ChanceFleeting/Fleeting_BMEDesign/Semester1Design/Electronics/FlowChart_v1.JPG

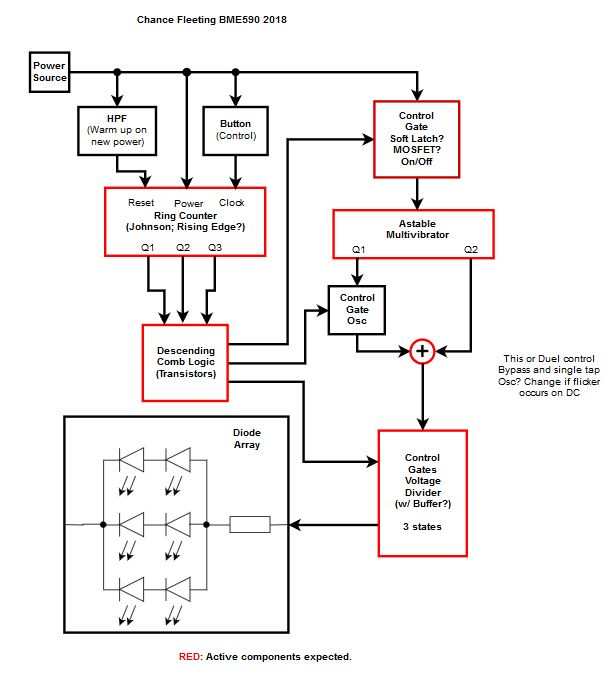
Semester1Design/Electronics/FlowChart_v1.JPG
