ChanceFleeting/Fleeting_BMEDesign/Semester1Design/Electronics/FlowChart_v2.jpg

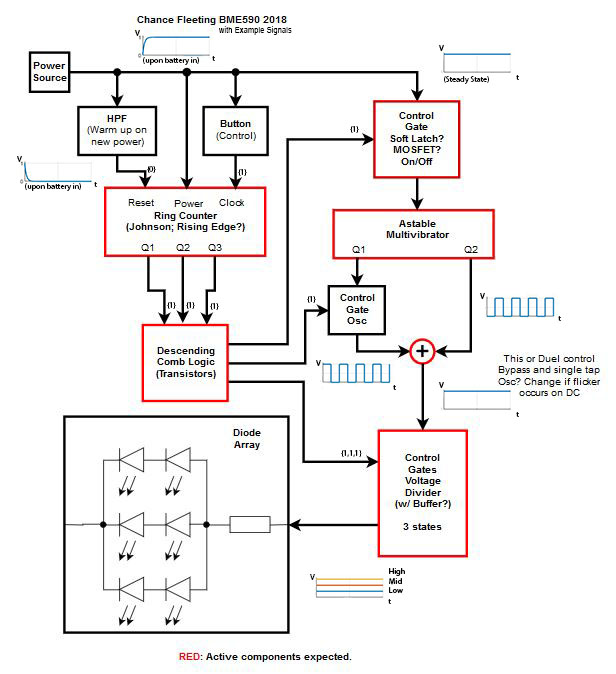
Semester1Design/Electronics/FlowChart_v2.jpg
