ChanceFleeting/Fleeting_BMEDesign/Semester1Design/Electronics/PCB/PCB_2D_Front.PNG

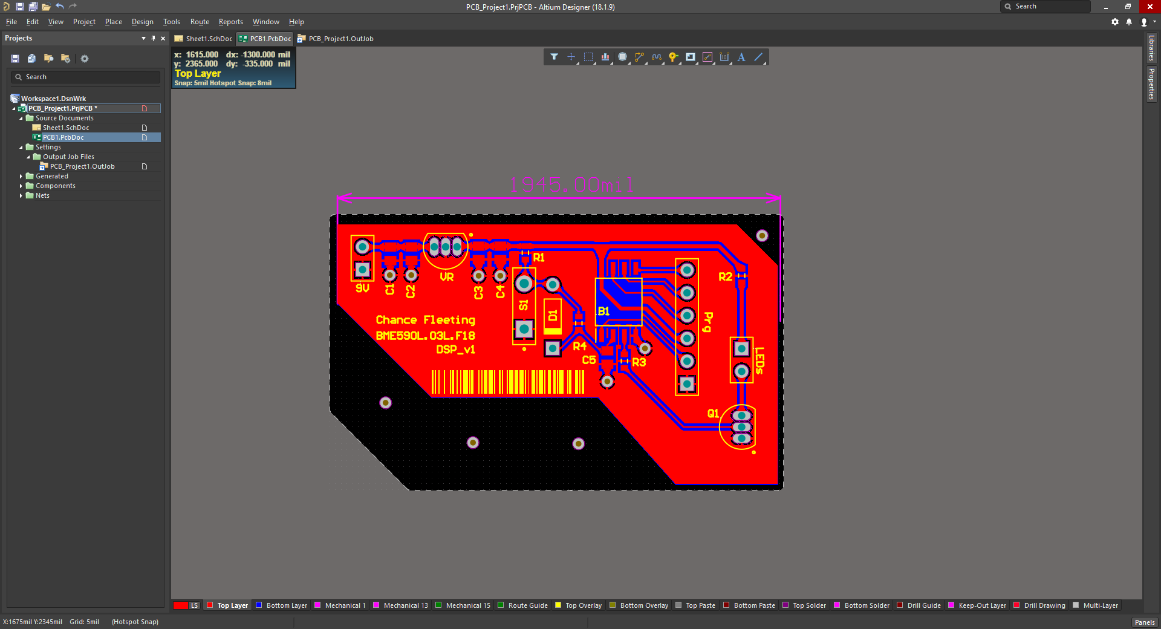
Semester1Design/Electronics/PCB/PCB_2D_Front.PNG
