ChanceFleeting/Fleeting_BMEDesign/Semester1Design/Electronics/PCB/PCB_2D_Front_smaller.PNG

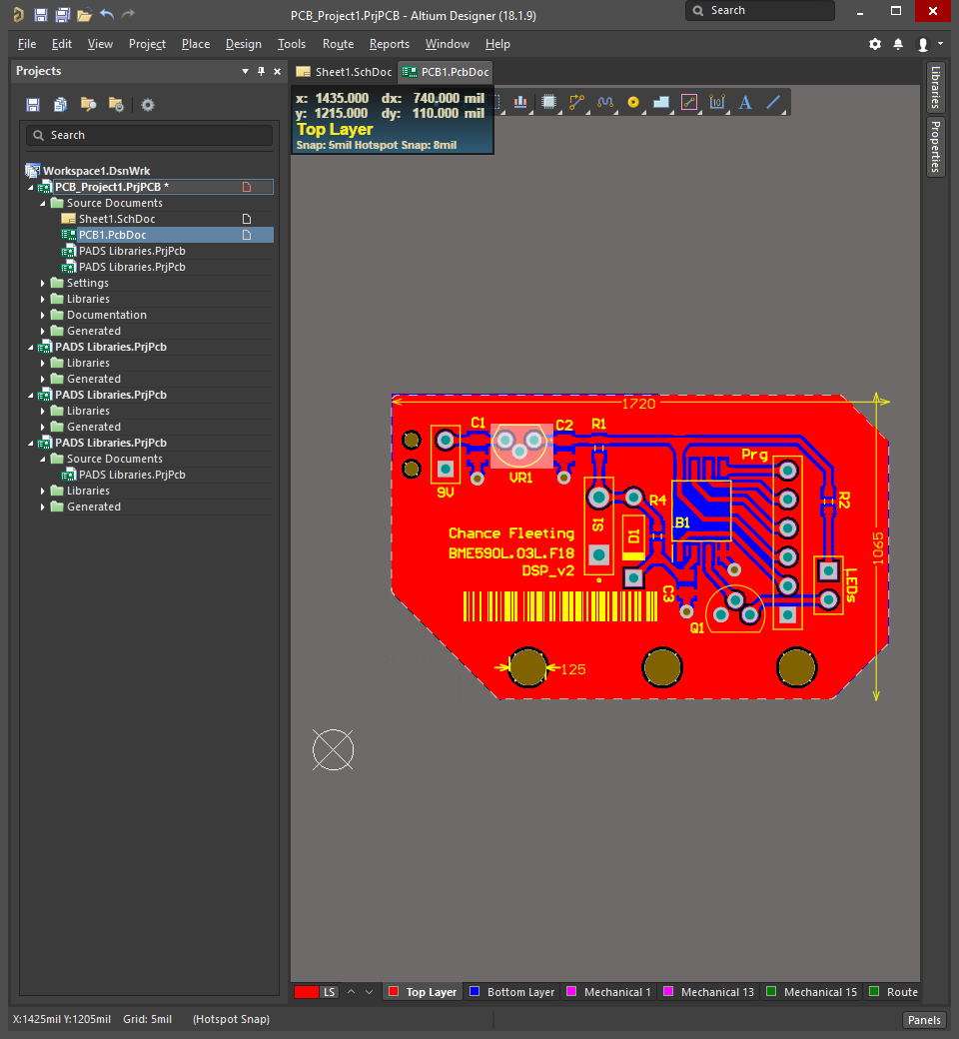
Semester1Design/Electronics/PCB/PCB_2D_Front_smaller.PNG
