ChanceFleeting/Fleeting_BMEDesign/Semester1Design/Electronics/PCB/PCB_3D_Back.PNG

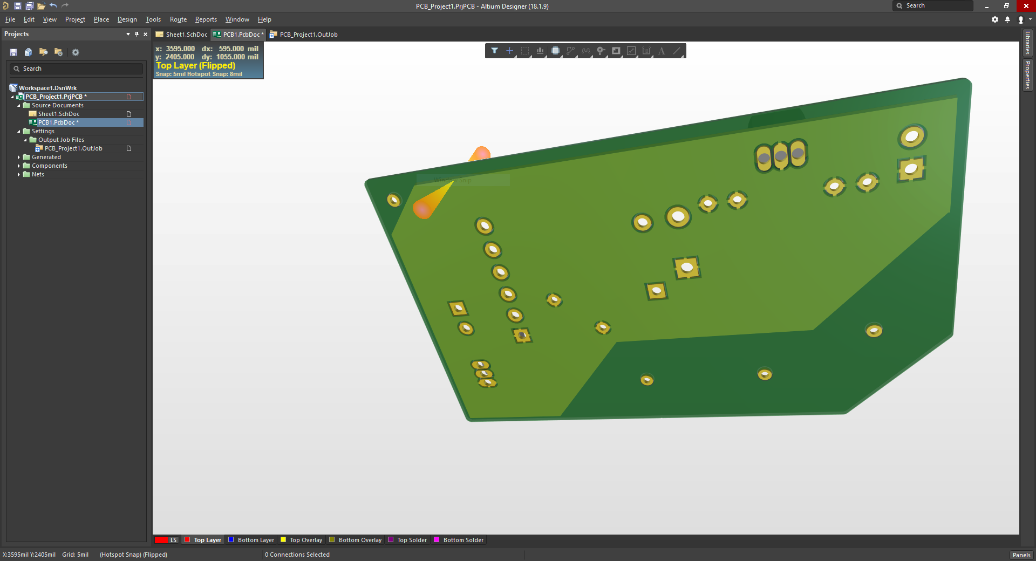
Semester1Design/Electronics/PCB/PCB_3D_Back.PNG
