ChanceFleeting/Fleeting_BMEDesign/Semester1Design/Electronics/PCB/PCB_3D_Back_smaller.PNG

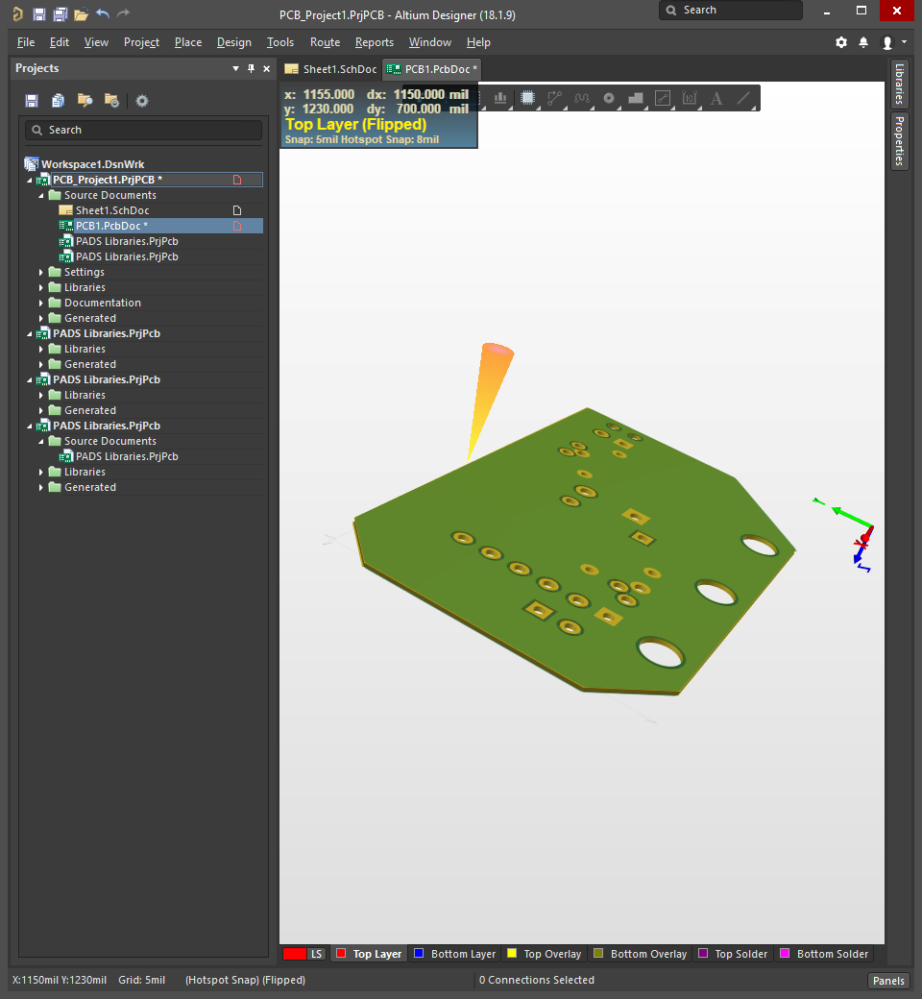
Semester1Design/Electronics/PCB/PCB_3D_Back_smaller.PNG
