ChanceFleeting/Fleeting_BMEDesign/Semester1Design/Mechanical/3Drendering.JPG

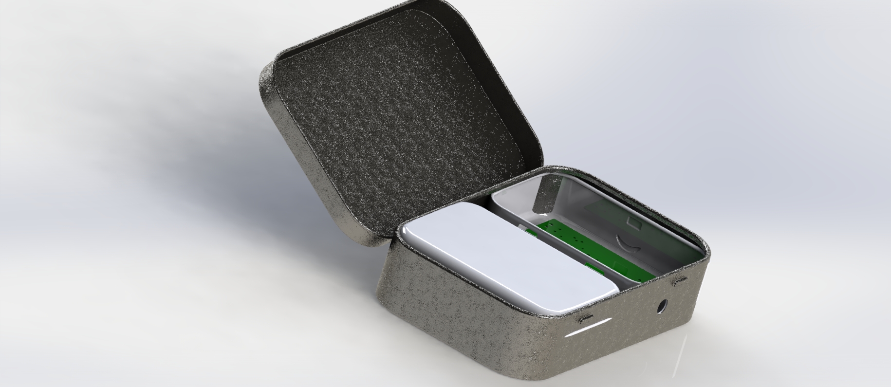
Semester1Design/Mechanical/3Drendering.JPG
