ChanceFleeting/Fleeting_BMEDesign/Semester1Design/Mechanical/MechSchem.jpeg

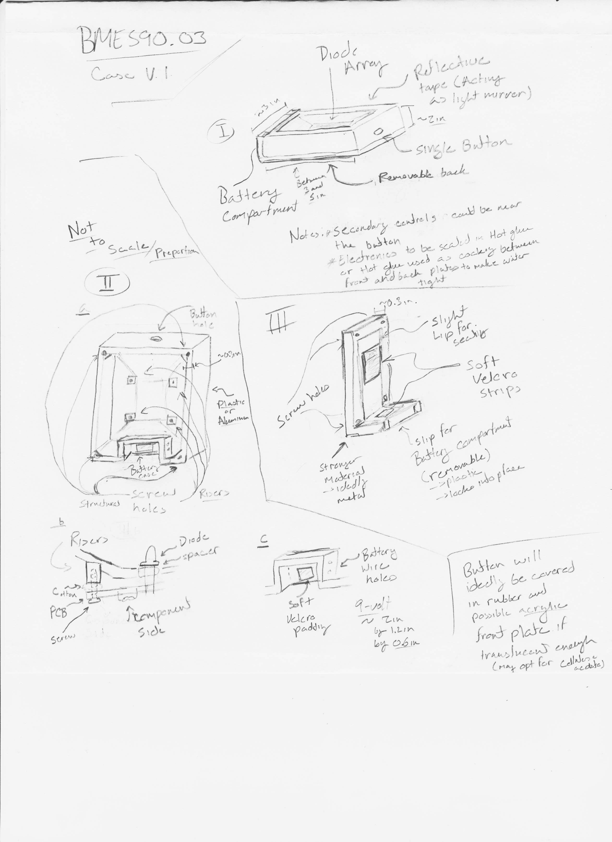
Semester1Design/Mechanical/MechSchem.jpeg
