ChanceFleeting/Fleeting_BMEDesign/Semester1Design/Software/CodingScheme1.PNG

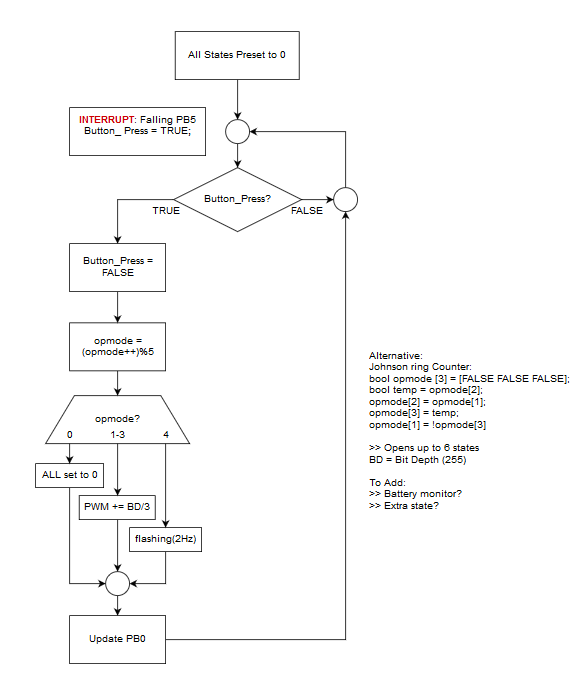
Semester1Design/Software/CodingScheme1.PNG
