ChanceFleeting/Fleeting_BMEDesign/Semester1Design/Testing/Final_Design_Large.jpg

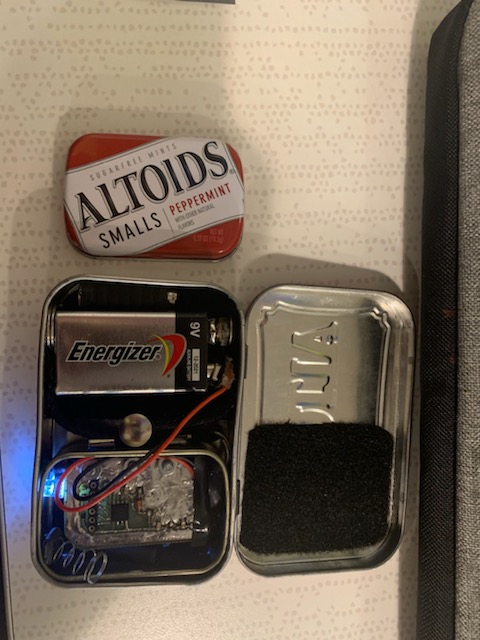
Semester1Design/Testing/Final_Design_Large.jpg
