ChanceFleeting/Fleeting_BMEDesign/Semester1Design/Testing/Final_Design_Large_2.jpg

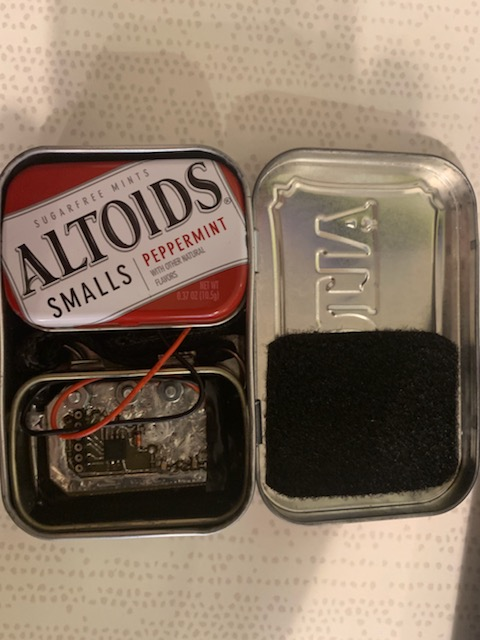
Semester1Design/Testing/Final_Design_Large_2.jpg
