ChanceFleeting/Fleeting_BMEDesign/Semester1Design/Testing/Final_Design_Small.jpg

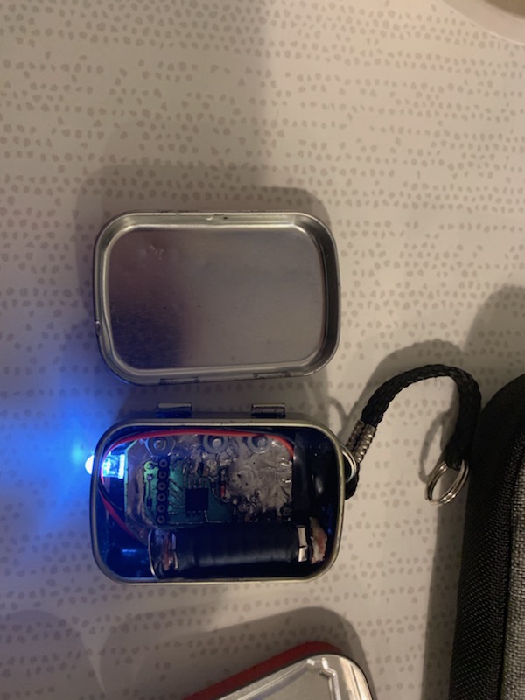
Semester1Design/Testing/Final_Design_Small.jpg
