ChanceFleeting/Fleeting_BMEDesign/Semester1Design/Testing/Final_Design_Small_2.jpg

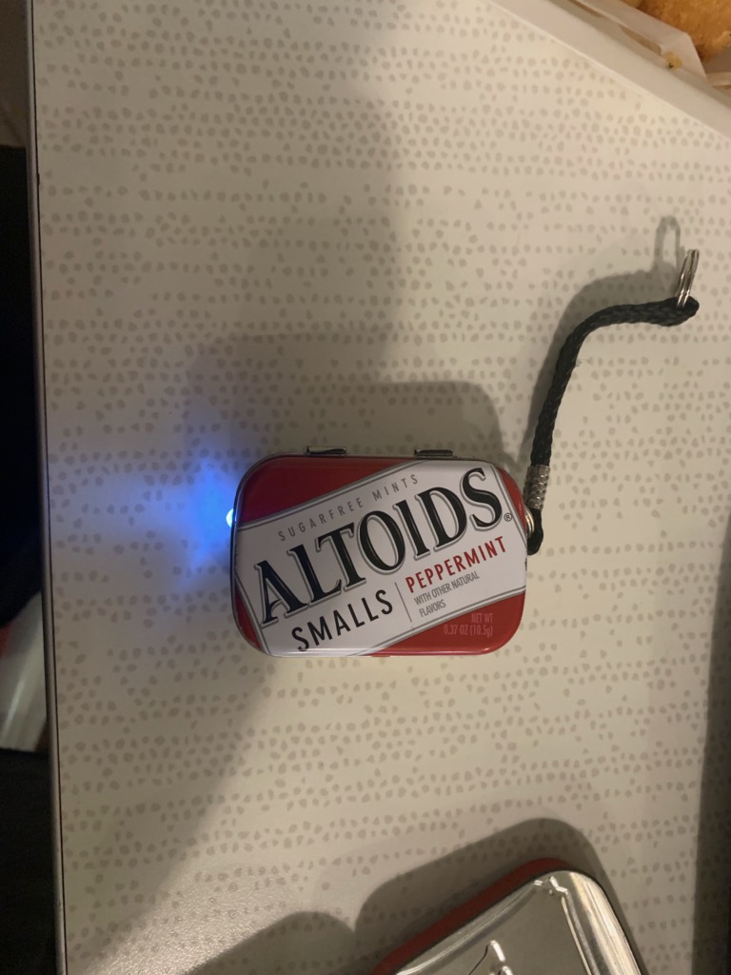
Semester1Design/Testing/Final_Design_Small_2.jpg
