ChanceFleeting/Fleeting_BMEDesign/Semester1Design/Testing/47579365_2035901176702119_994453910217293824_n.jpg

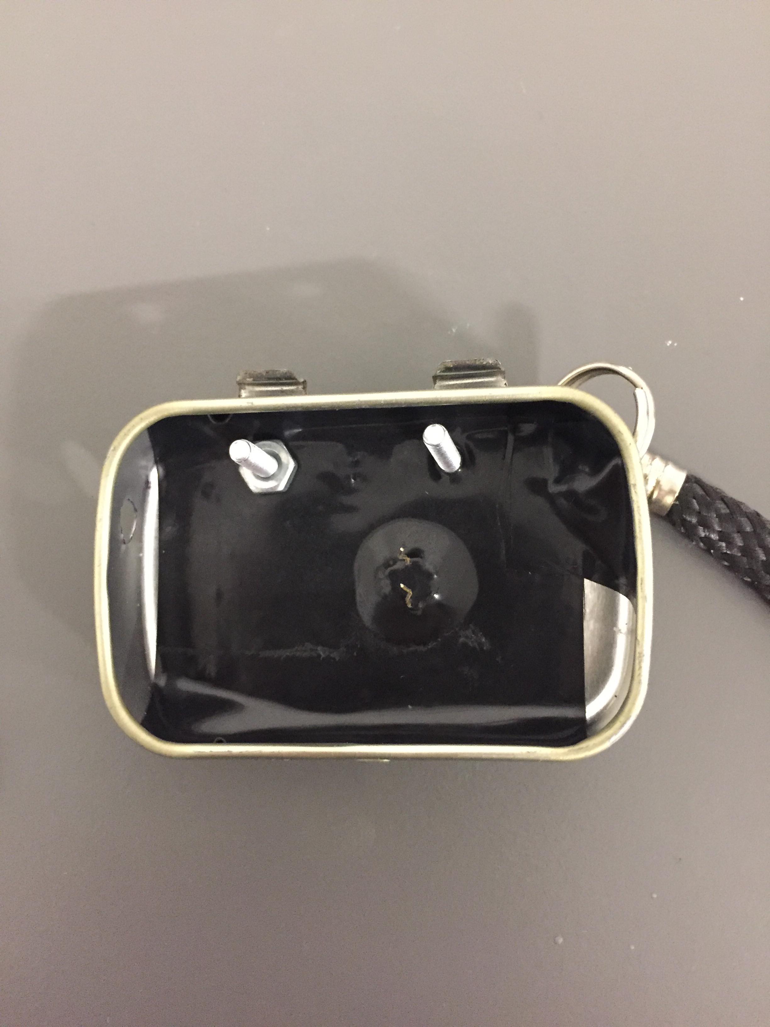
Semester1Design/Testing/47579365_2035901176702119_994453910217293824_n.jpg
