ChanceFleeting/Fleeting_BMEDesign/Semester1Design/Testing/47679753_585677868552466_7844225675530600448_n.jpg

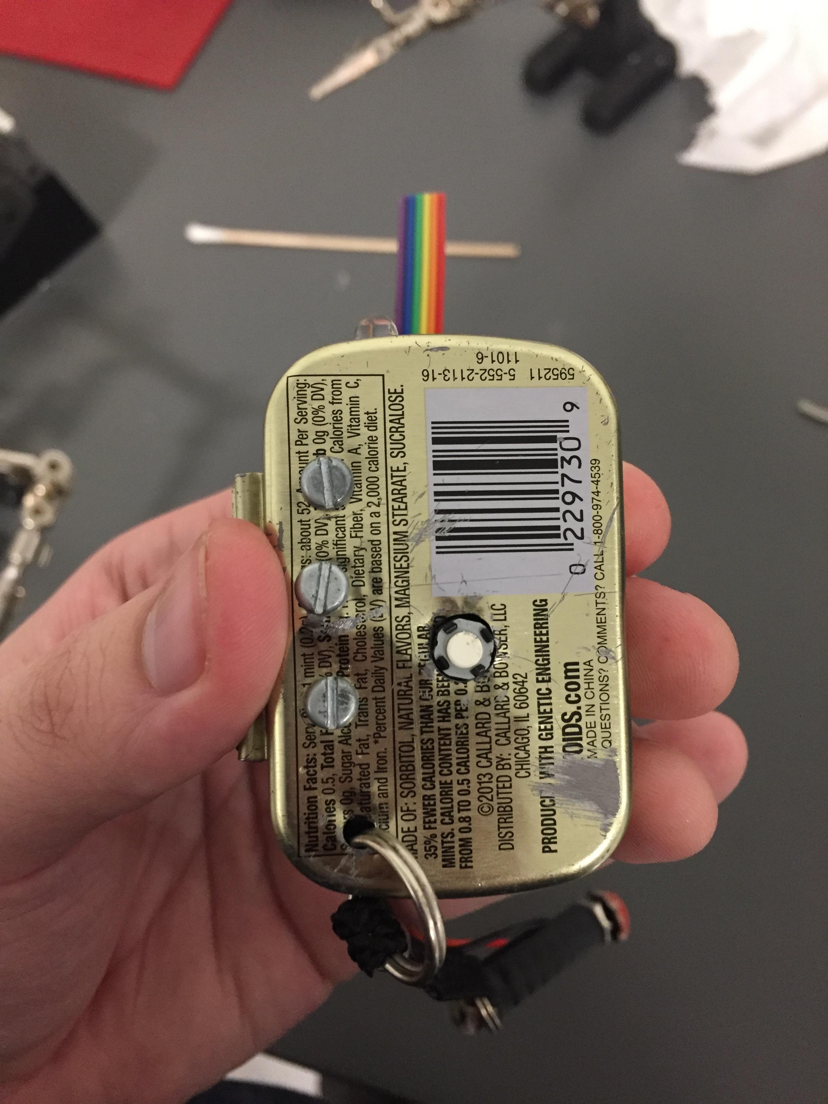
Semester1Design/Testing/47679753_585677868552466_7844225675530600448_n.jpg
