ChanceFleeting/Fleeting_BMEDesign/Semester1Design/Testing/47681514_1208115799335710_4562867139513417728_n.jpg

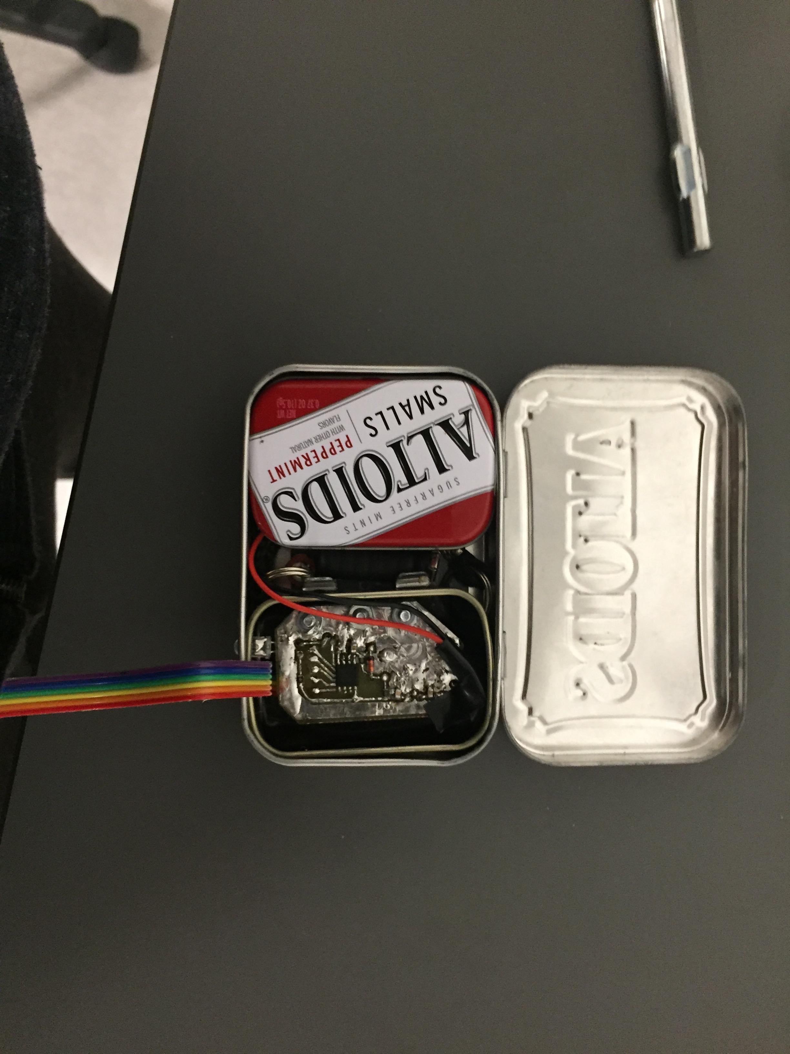
Semester1Design/Testing/47681514_1208115799335710_4562867139513417728_n.jpg
