ChanceFleeting/Fleeting_BMEDesign/Semester1Design/Testing/47684558_2132880680297586_8307508305803083776_n.jpg

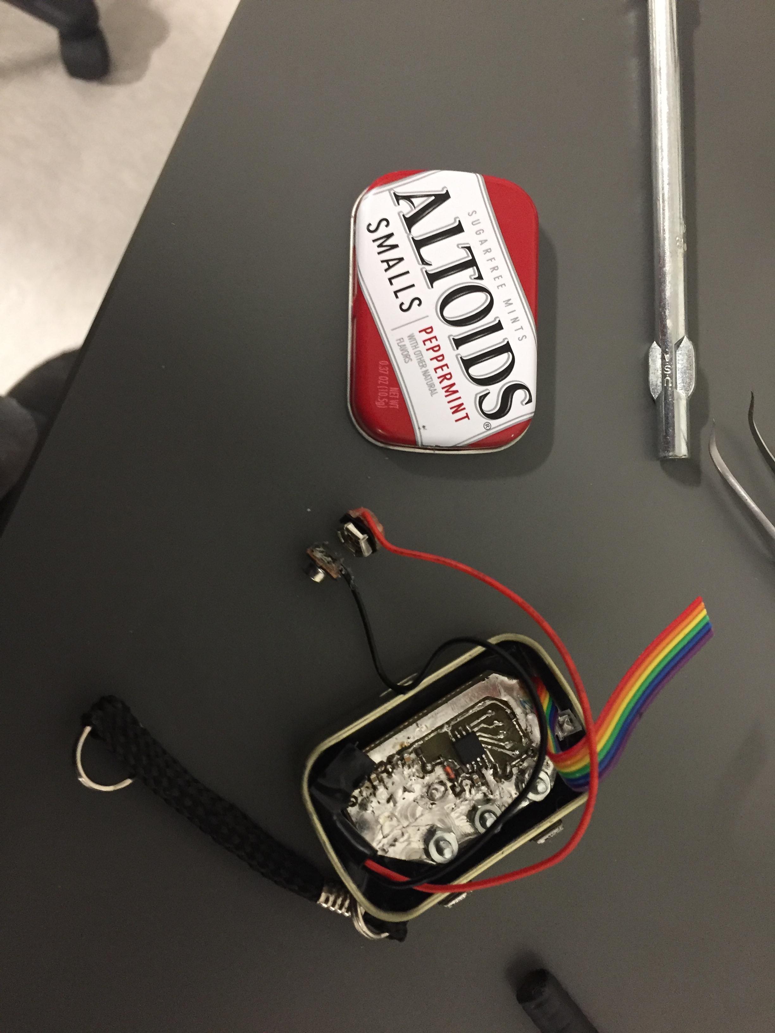
Semester1Design/Testing/47684558_2132880680297586_8307508305803083776_n.jpg
