ChanceFleeting/Fleeting_BMEDesign/Semester1Design/Testing/47687072_275529913152030_7336165631785435136_n.jpg

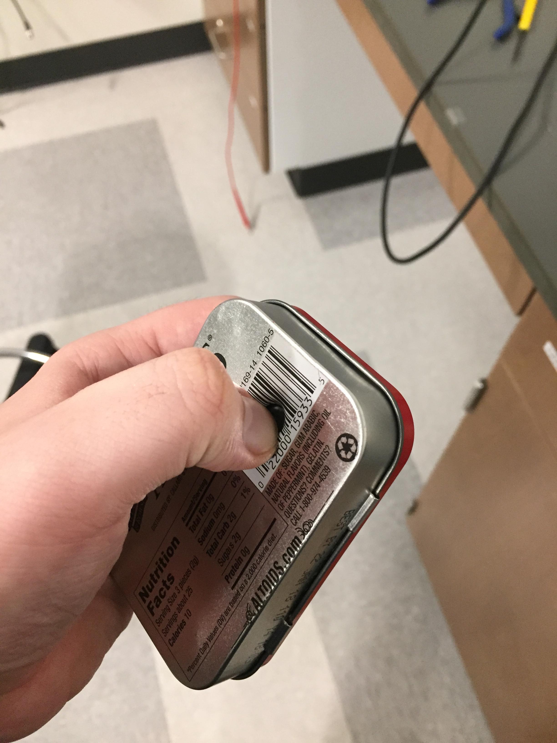
Semester1Design/Testing/47687072_275529913152030_7336165631785435136_n.jpg
