ChanceFleeting/Fleeting_BMEDesign/Semester1Design/Testing/47687882_234557353955737_6065184194995159040_n.jpg

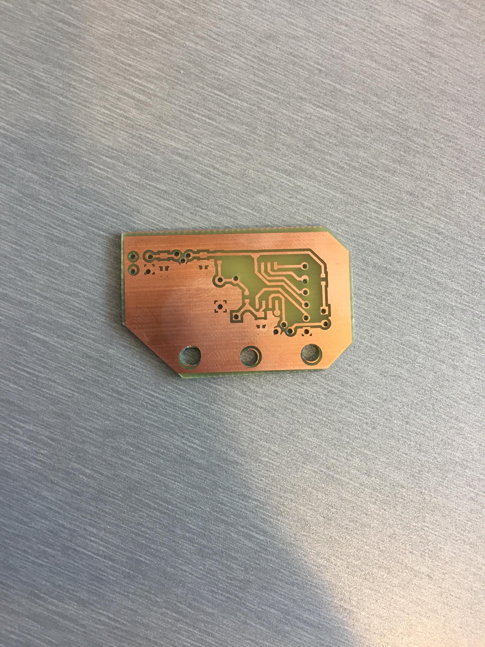
Semester1Design/Testing/47687882_234557353955737_6065184194995159040_n.jpg
