ChanceFleeting/Fleeting_BMEDesign/Semester1Design/Testing/47688594_2274070586161696_6565518919719714816_n.jpg

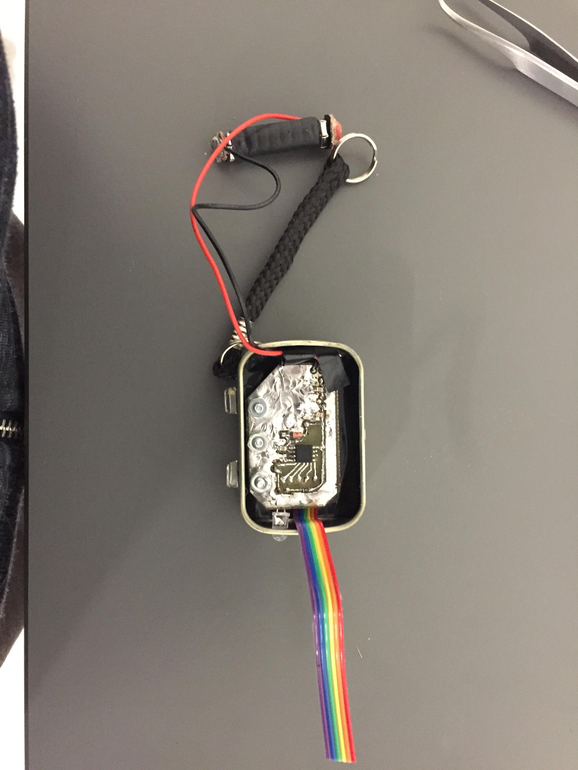
Semester1Design/Testing/47688594_2274070586161696_6565518919719714816_n.jpg
