ChanceFleeting/Fleeting_BMEDesign/Semester1Design/Testing/48360756_349484335630814_5240922371086352384_n.jpg

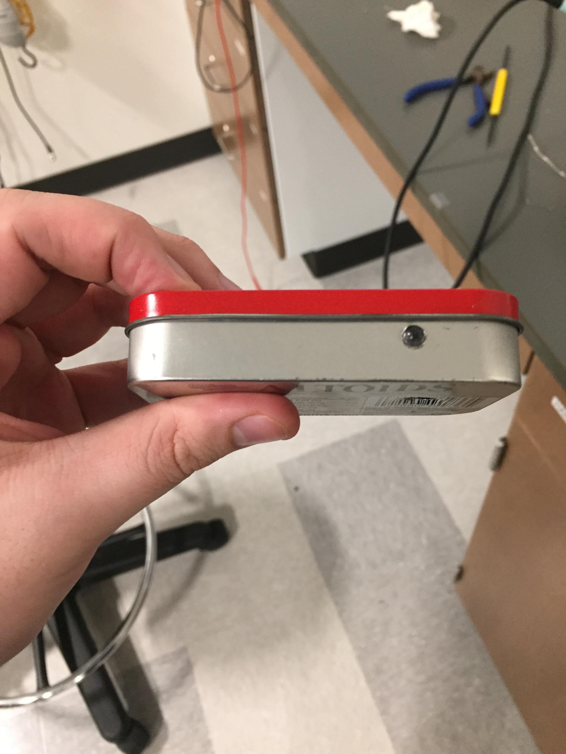
Semester1Design/Testing/48360756_349484335630814_5240922371086352384_n.jpg
