ChanceFleeting/Fleeting_BMEDesign/Semester1Design/Testing/48370219_289954611647811_1946431835122696192_n.jpg

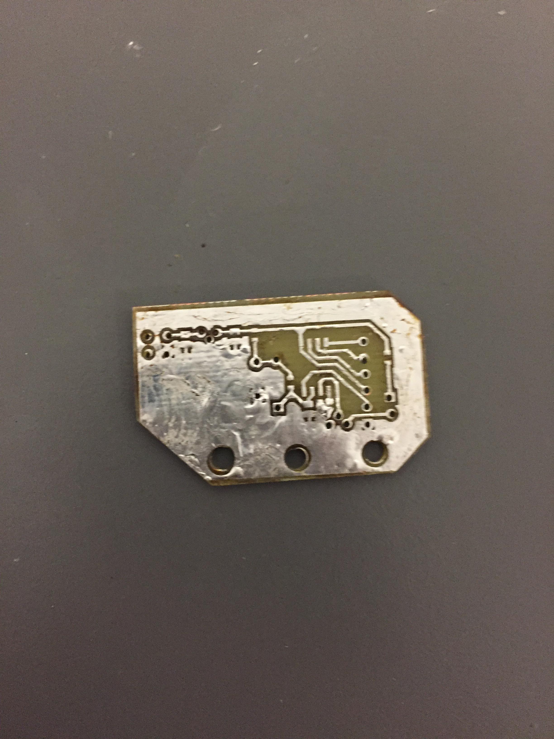
Semester1Design/Testing/48370219_289954611647811_1946431835122696192_n.jpg
