ChanceFleeting/Fleeting_BMEDesign/Semester1Design/Testing/48379618_350906905704294_4877027714994798592_n.jpg

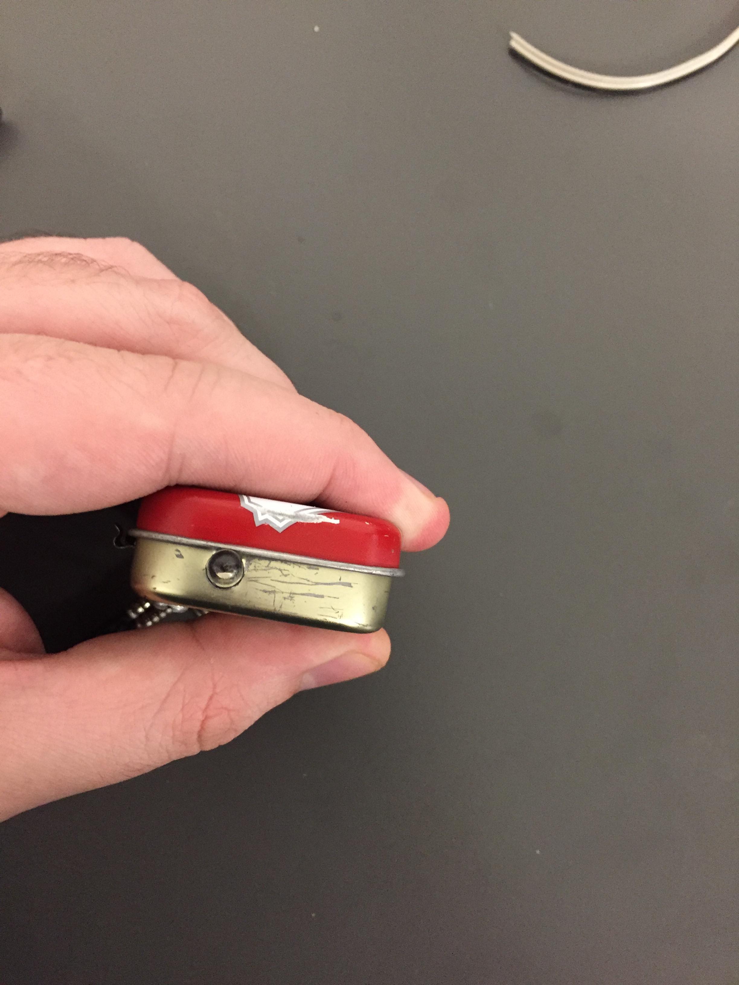
Semester1Design/Testing/48379618_350906905704294_4877027714994798592_n.jpg
