ChanceFleeting/Fleeting_BMEDesign/Semester1Design/Testing/Demos/6cellLR41Battery.jpg

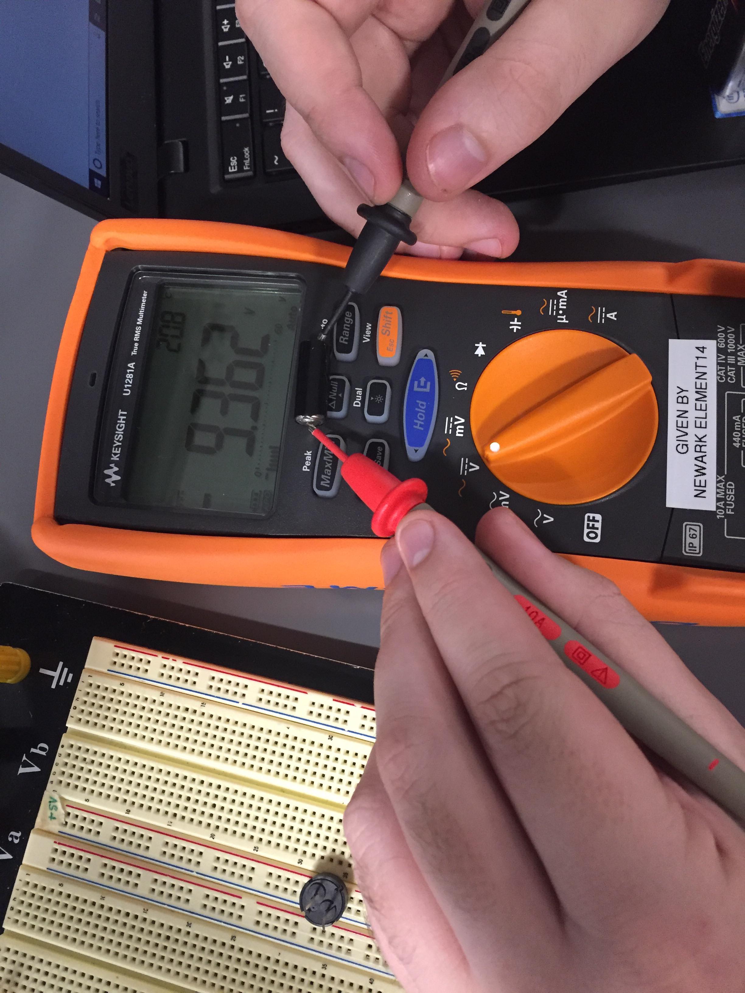
Semester1Design/Testing/Demos/6cellLR41Battery.jpg
