ChanceFleeting/Fleeting_BMEDesign/Semester1Design/Testing/Demos/Debounce_Asym_lowpass.jpg

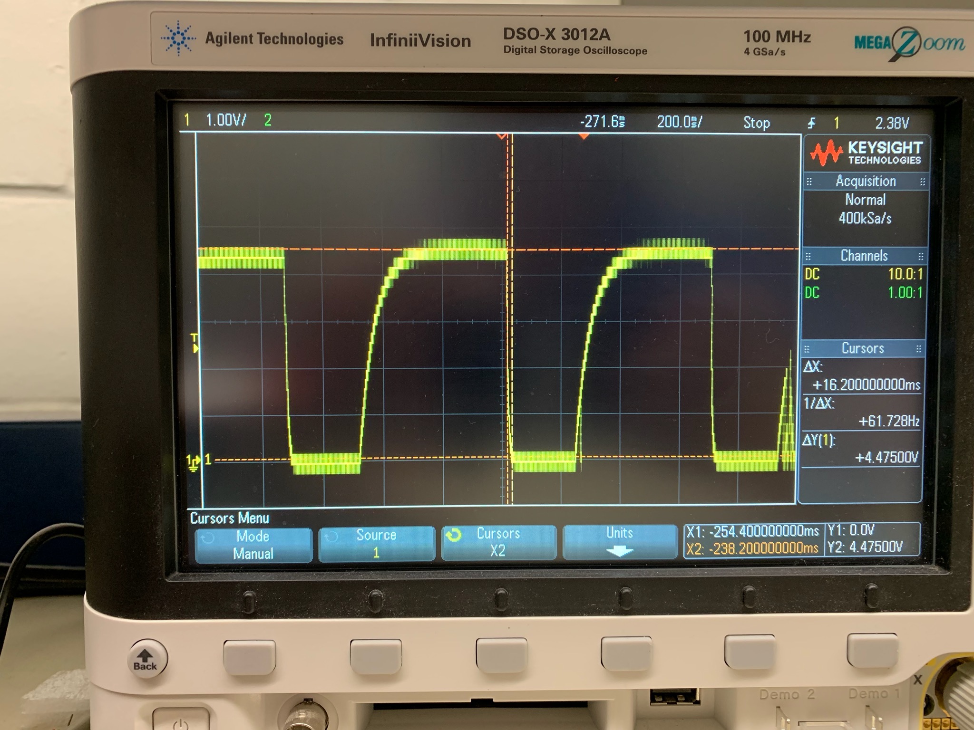
Semester1Design/Testing/Demos/Debounce_Asym_lowpass.jpg
