ChanceFleeting/Fleeting_BMEDesign/Semester1Design/Testing/IMG_0030.jpg

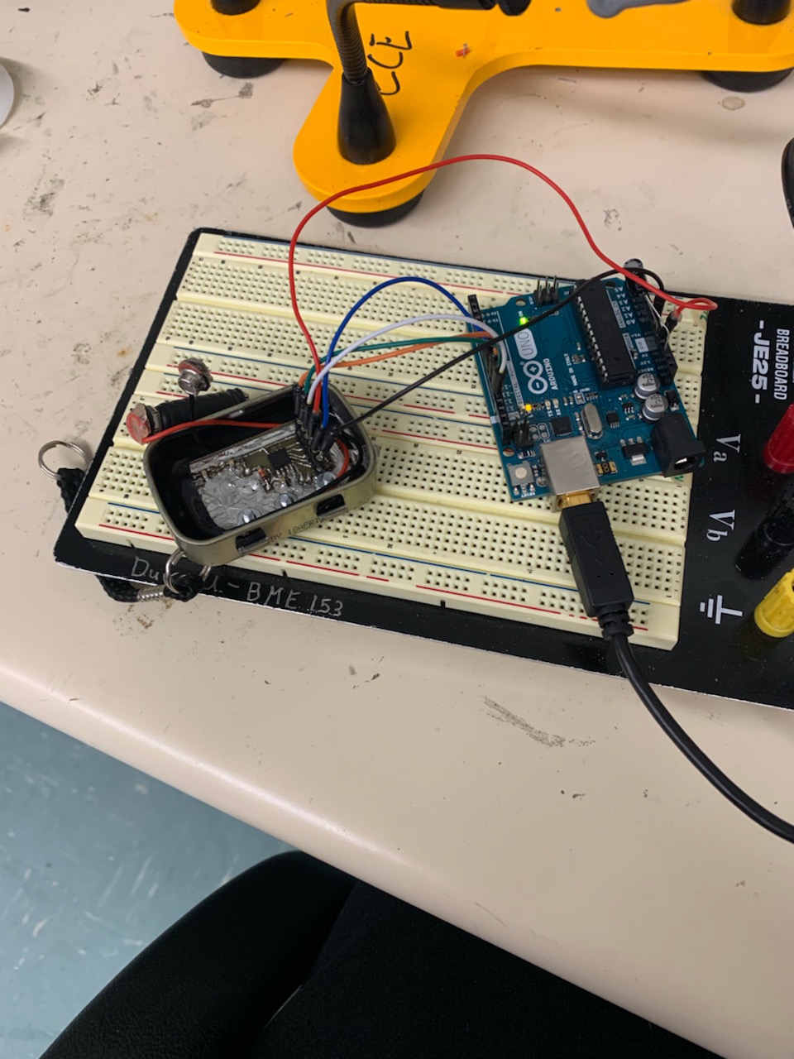
Semester1Design/Testing/IMG_0030.jpg
