ChanceFleeting/Fleeting_BMEDesign/Semester1Design/Testing/IMG_0031.jpg

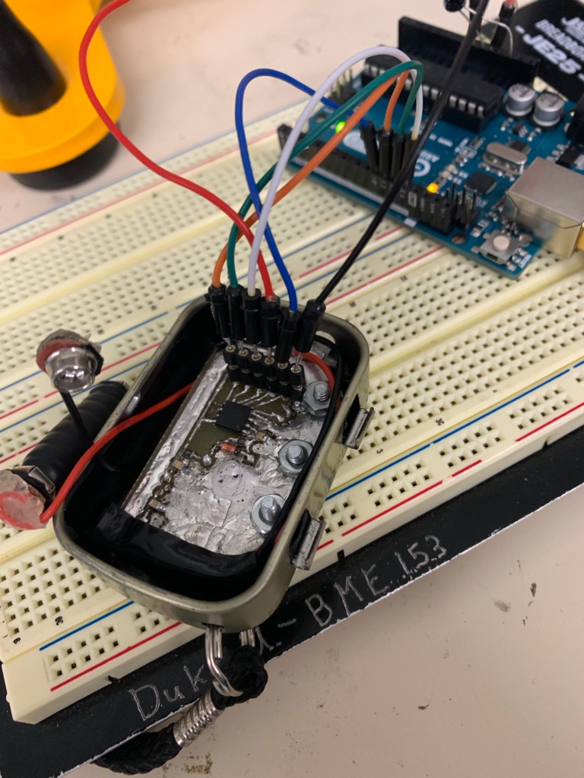
Semester1Design/Testing/IMG_0031.jpg
