ChanceFleeting/Fleeting_BMEDesign/Semester1Design/Testing/IMG_0032.jpg

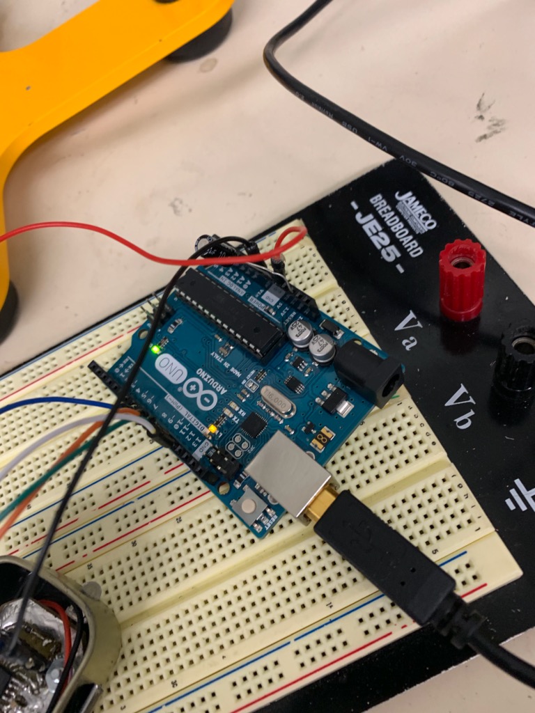
Semester1Design/Testing/IMG_0032.jpg
