ChanceFleeting/Fleeting_BMEDesign/Semester1Design/Electronics/PCB/ECAD files/Sheet1.pdf

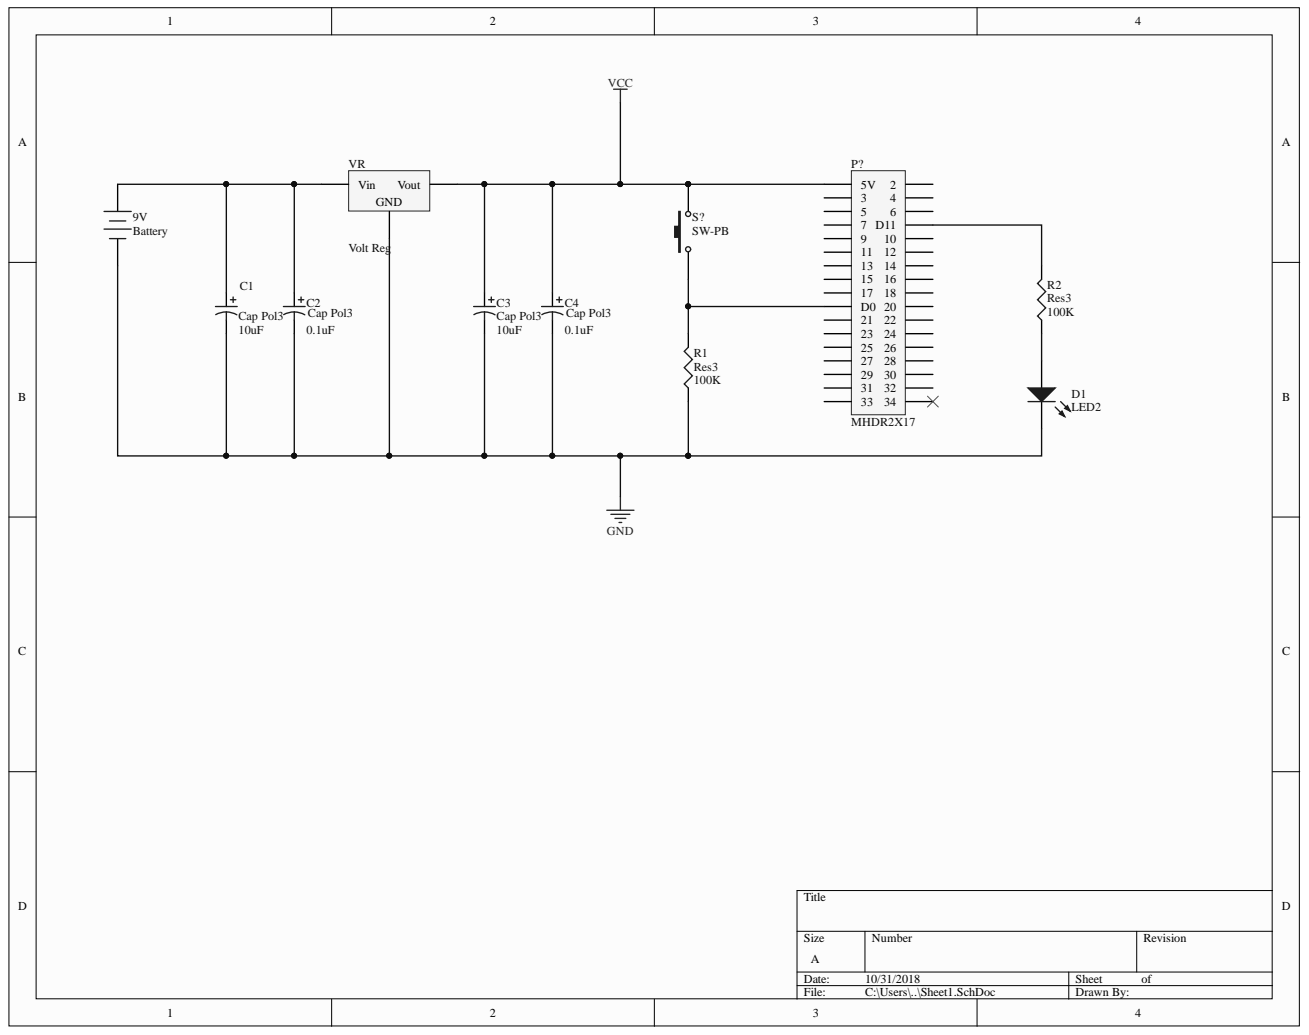
[picture p51: page 1]

# Board S
